alpd11/Bond_Note/3D_model/IMG/iteration.jpg

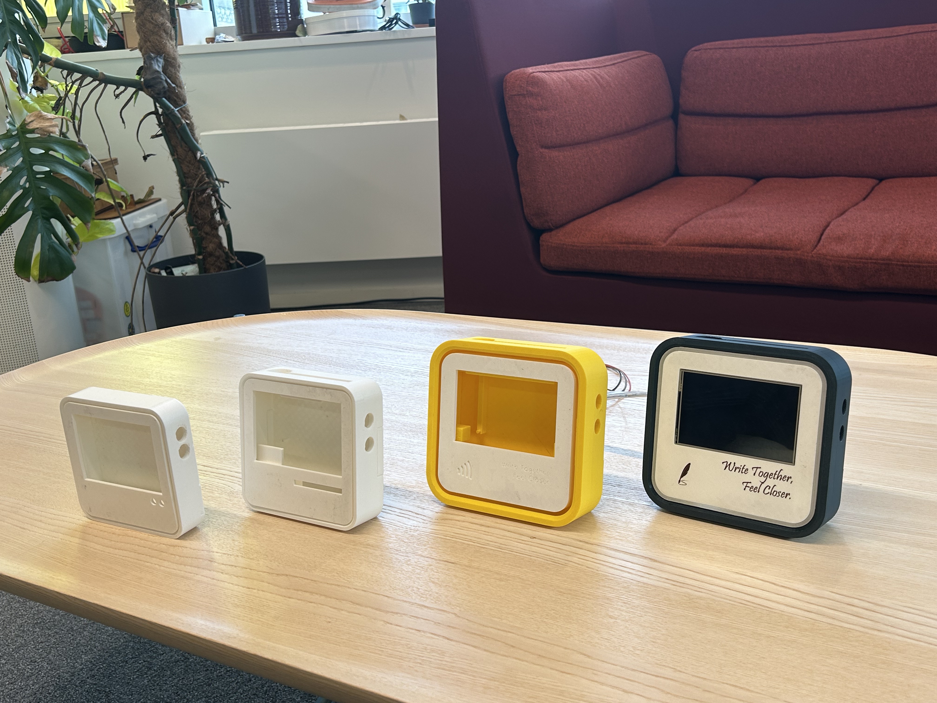
3D_model/IMG/iteration.jpg
