alpd11/Bond_Note/3D_model/IMG/sketch2.jpg

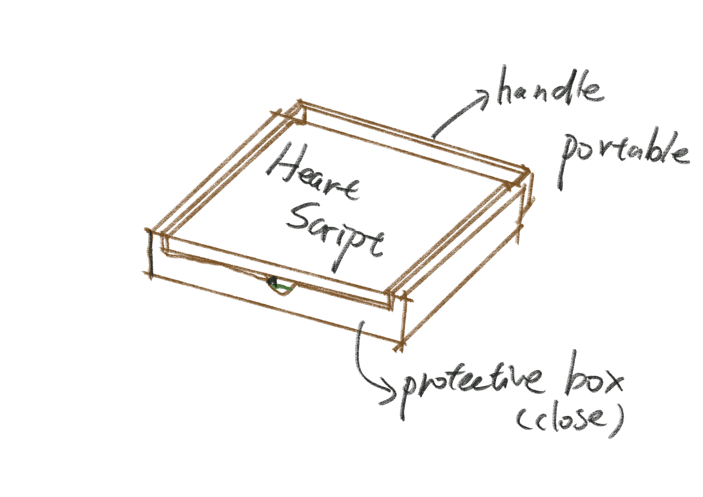
3D_model/IMG/sketch2.jpg
